cepdnaclk/e21-3yp-SlideSense/docs/assets/about/about-slidesense.png

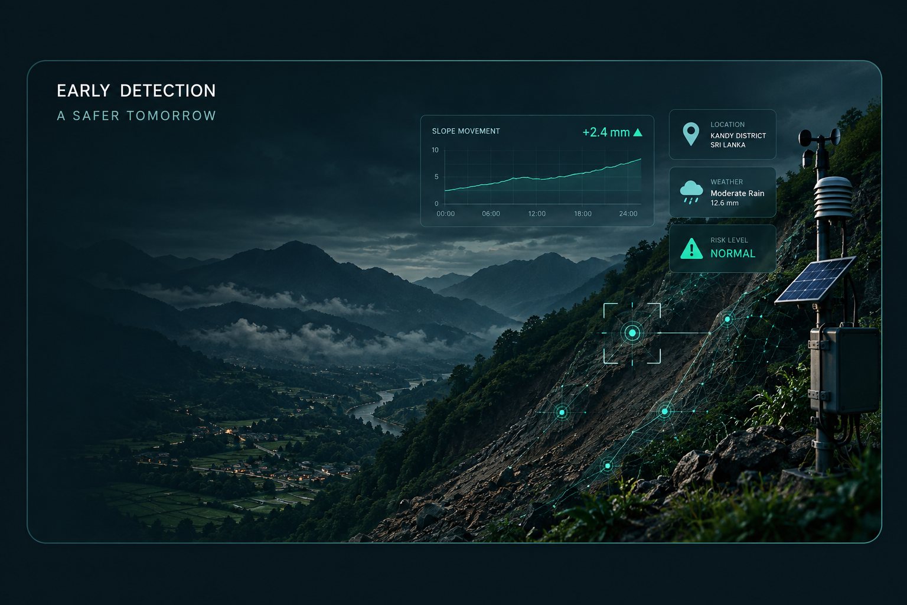
docs/assets/about/about-slidesense.png
