cepdnaclk/e21-3yp-SlideSense/docs/assets/Compenents/aws-iot-core.png

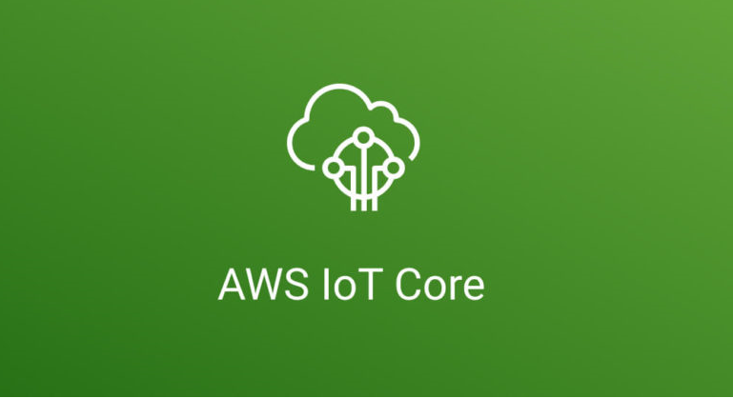
docs/assets/Compenents/aws-iot-core.png
