cepdnaclk/e21-3yp-SlideSense/docs/assets/Compenents/esp32.jpg

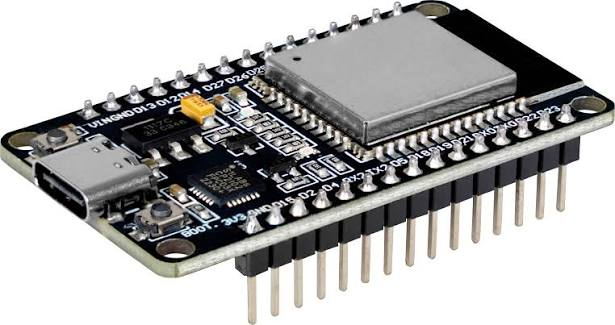
docs/assets/Compenents/esp32.jpg
