cepdnaclk/e21-3yp-SlideSense/docs/assets/Compenents/GPS_module.jpg

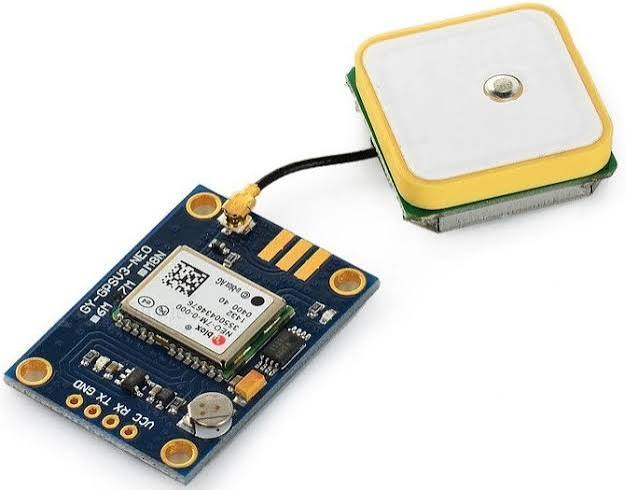
docs/assets/Compenents/GPS_module.jpg
