cepdnaclk/e21-3yp-SlideSense/docs/assets/Compenents/microphone.jpg

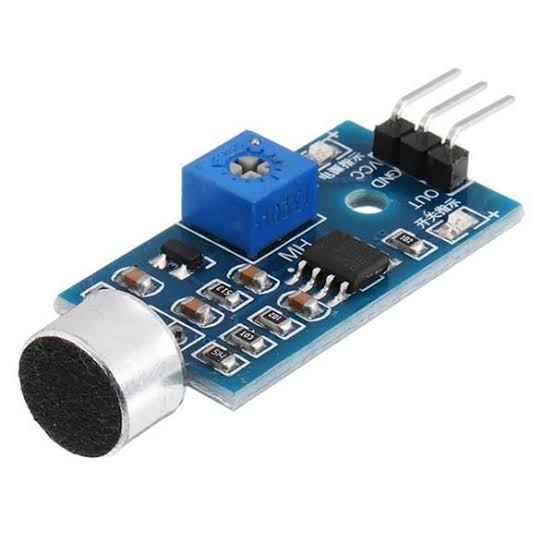
docs/assets/Compenents/microphone.jpg
