cepdnaclk/e21-3yp-SlideSense/docs/assets/Compenents/soli-moisture.jpg

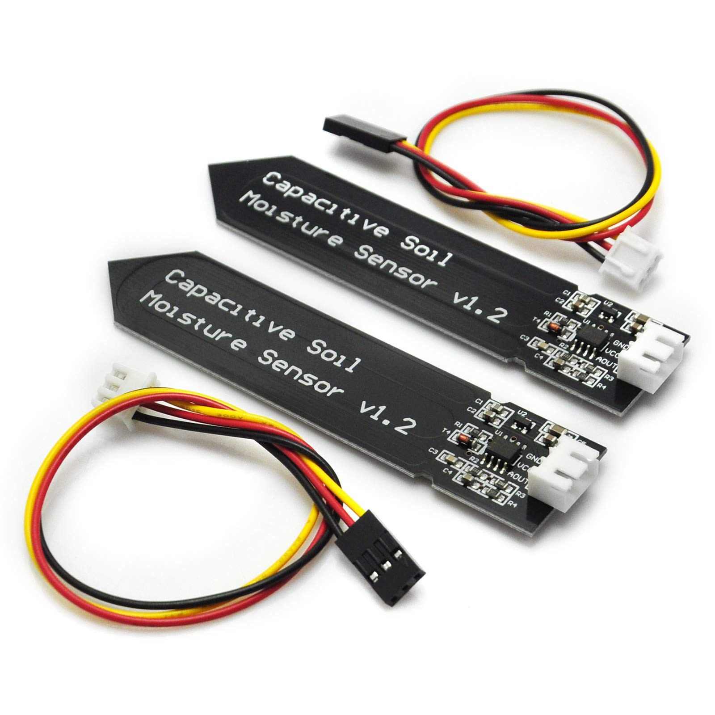
docs/assets/Compenents/soli-moisture.jpg
