cepdnaclk/e21-3yp-SlideSense/docs/assets/Compenents/tilt_sesnsor.webp

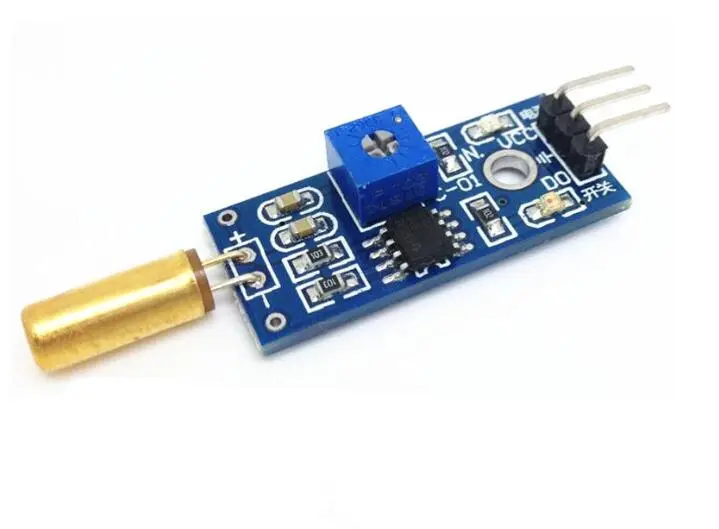
docs/assets/Compenents/tilt_sesnsor.webp
