cepdnaclk/e21-3yp-SlideSense/docs/assets/dashboard/image.png

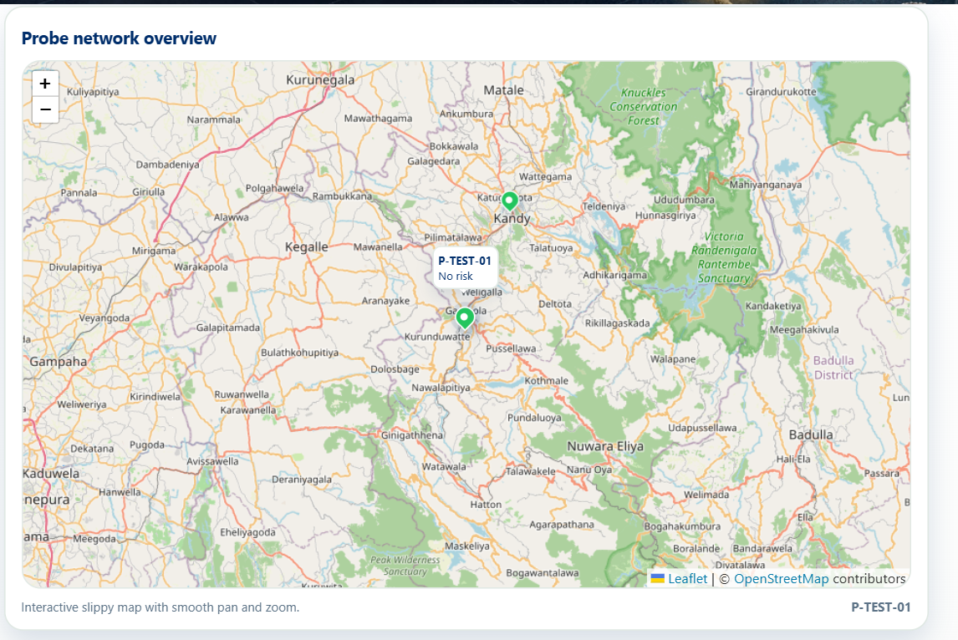
docs/assets/dashboard/image.png
