cepdnaclk/e21-3yp-SlideSense/docs/assets/dashboard/main.png

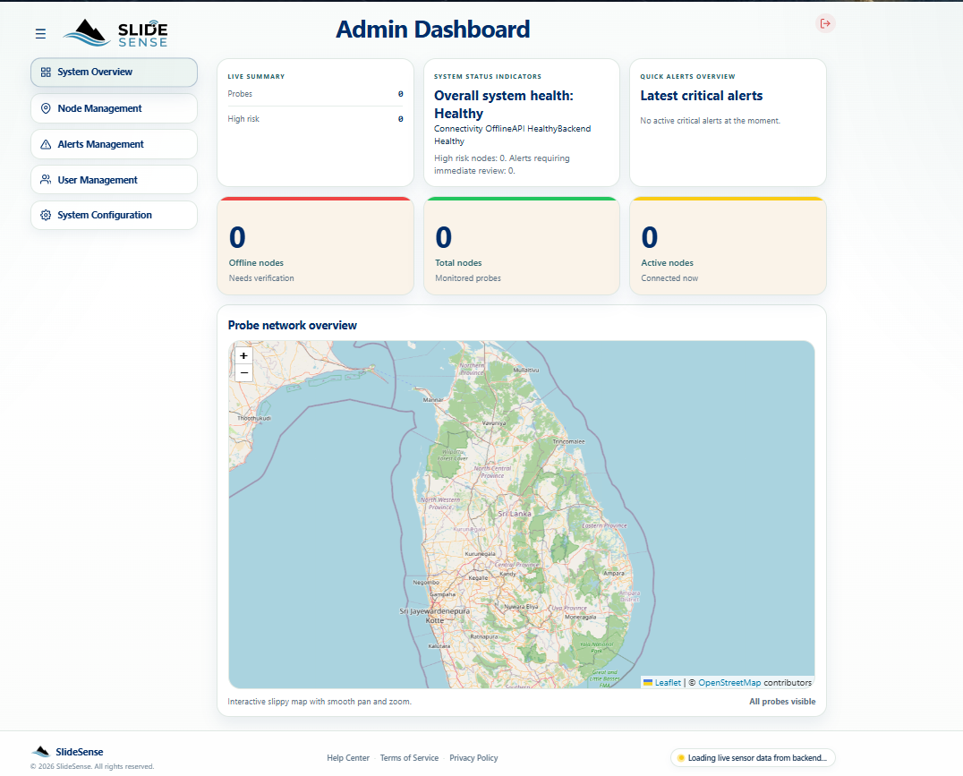
docs/assets/dashboard/main.png
