cepdnaclk/e21-3yp-SlideSense/docs/assets/final_product/probe.png

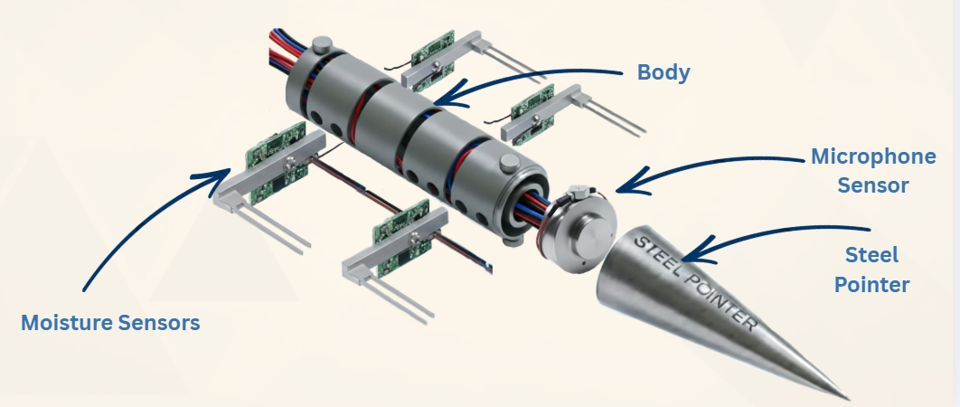
docs/assets/final_product/probe.png
