cepdnaclk/e21-3yp-SlideSense/docs/assets/final_product/solar.jpeg

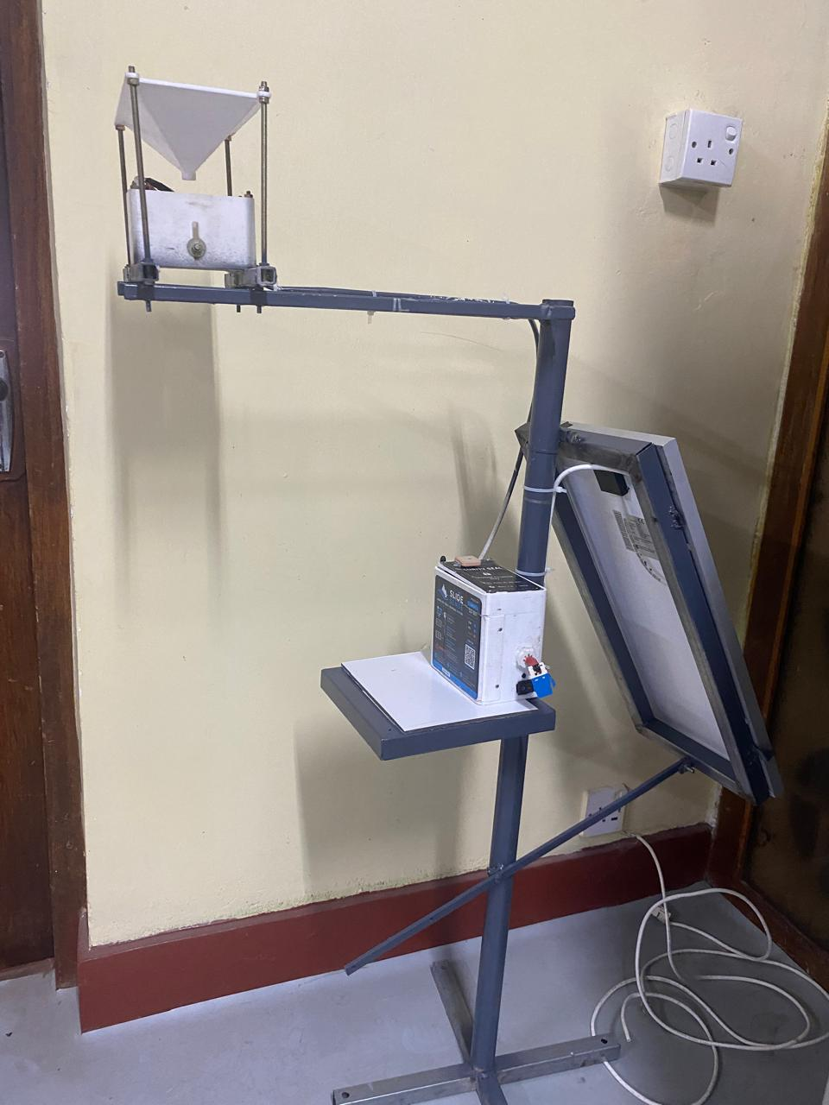
docs/assets/final_product/solar.jpeg
