cepdnaclk/e21-3yp-SlideSense/docs/assets/hero-background.png

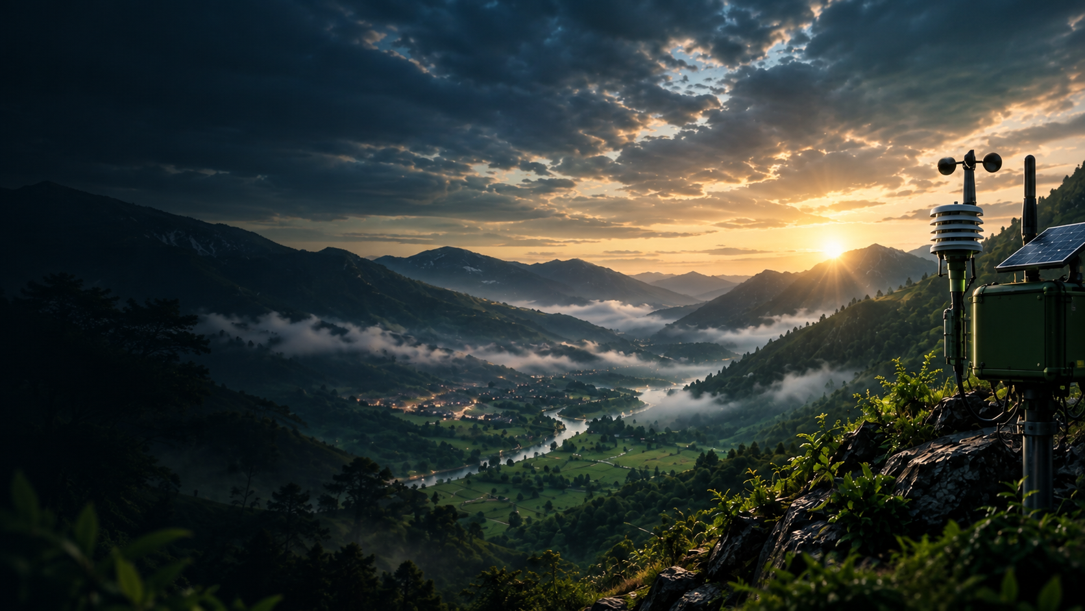
docs/assets/hero-background.png
