cepdnaclk/e21-3yp-SlideSense/docs/assets/images/historical_sensor_analytics.png

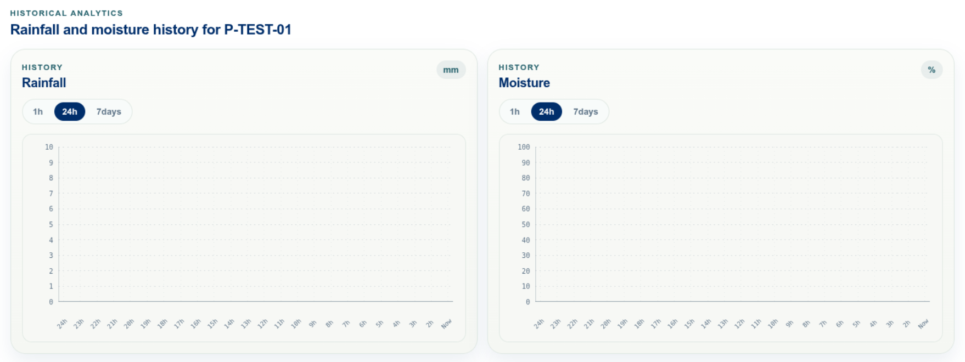
docs/assets/images/historical_sensor_analytics.png
