cepdnaclk/e21-3yp-SlideSense/docs/assets/images/hole.jpeg

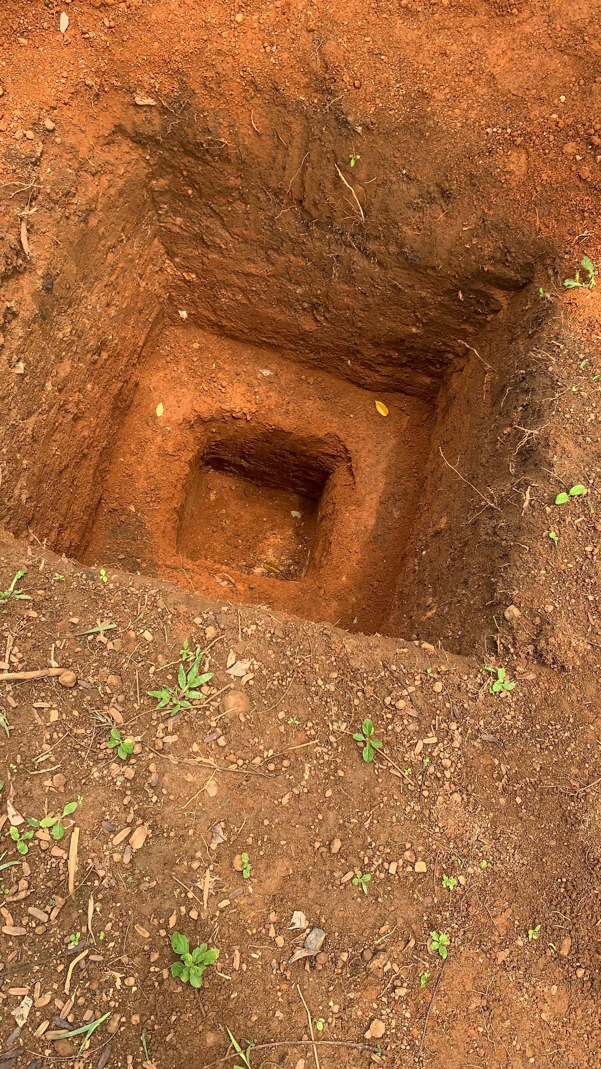
docs/assets/images/hole.jpeg
