cepdnaclk/e21-3yp-SlideSense/docs/assets/images/probe_in_hole.jpeg

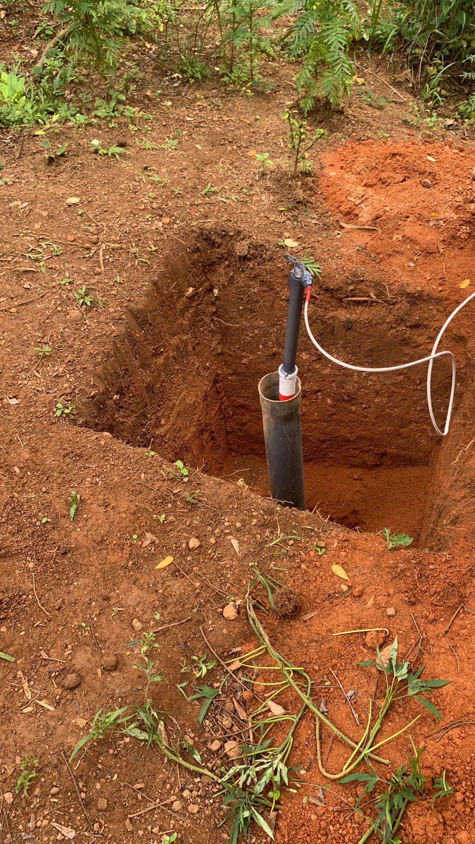
docs/assets/images/probe_in_hole.jpeg
