cepdnaclk/e21-3yp-SlideSense/docs/assets/images/rain_gauge.jpeg

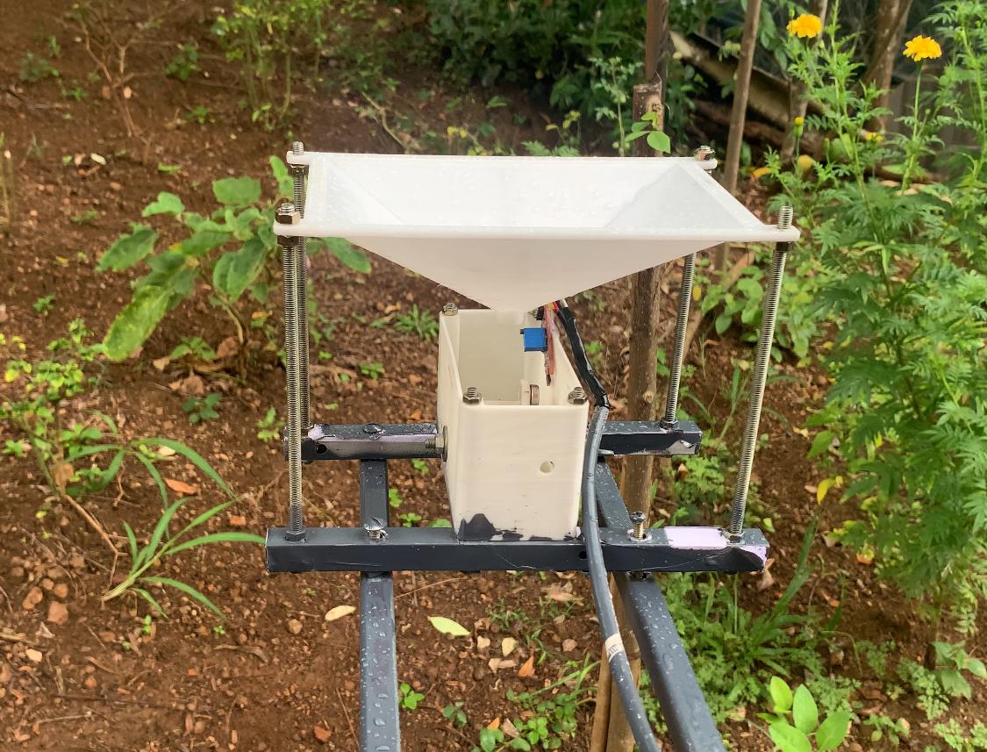
docs/assets/images/rain_gauge.jpeg
