cepdnaclk/e21-3yp-SlideSense/docs/assets/images/team_final.jpeg

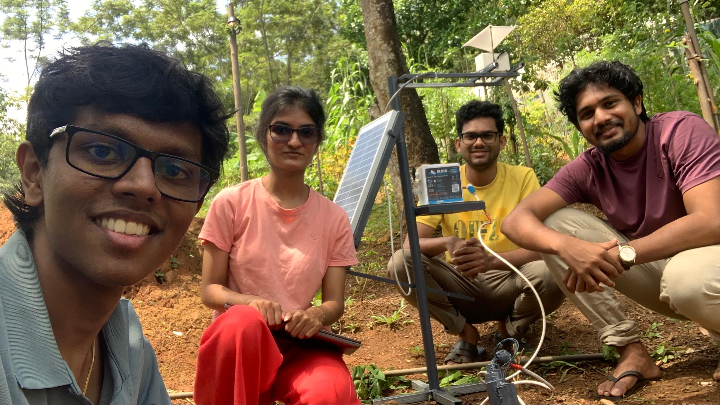
docs/assets/images/team_final.jpeg
