cepdnaclk/e21-3yp-SlideSense/docs/assets/images/work_bench_1.jpeg

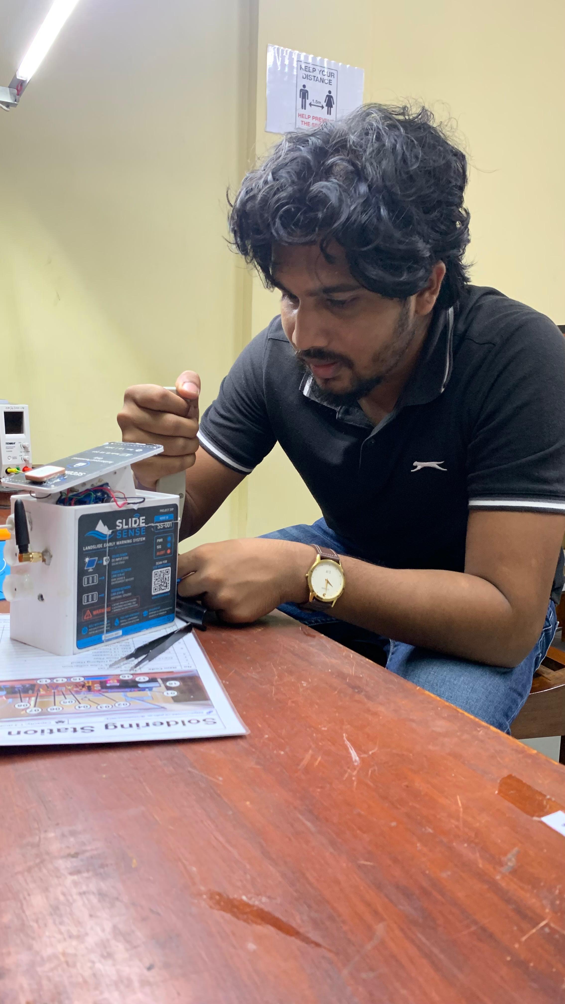
docs/assets/images/work_bench_1.jpeg
