cepdnaclk/e21-3yp-SlideSense/docs/assets/LoadBackground.jpg

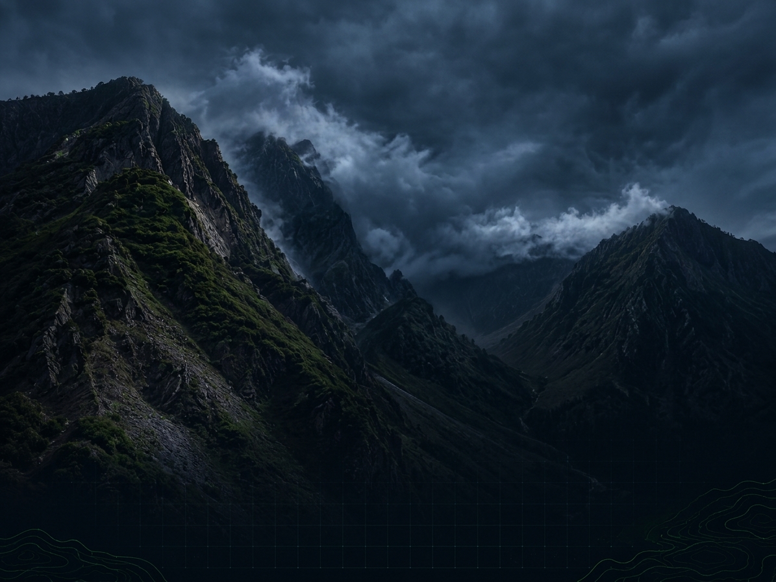
docs/assets/LoadBackground.jpg
