cepdnaclk/e21-3yp-SlideSense/docs/assets/videos/WhatsApp Image 2026-09-15 at 19.24.26.jpeg

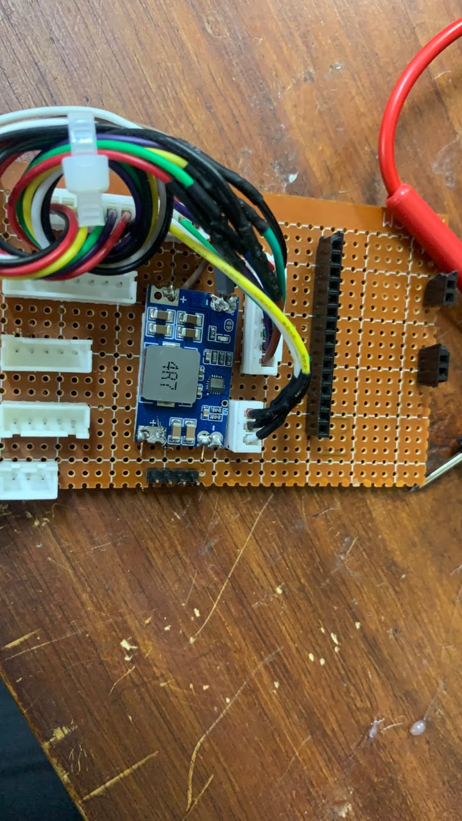
docs/assets/videos/WhatsApp Image 2026-09-15 at 19.24.26.jpeg
