cepdnaclk/e21-3yp-SlideSense/docs/data/thumbnail.jpg

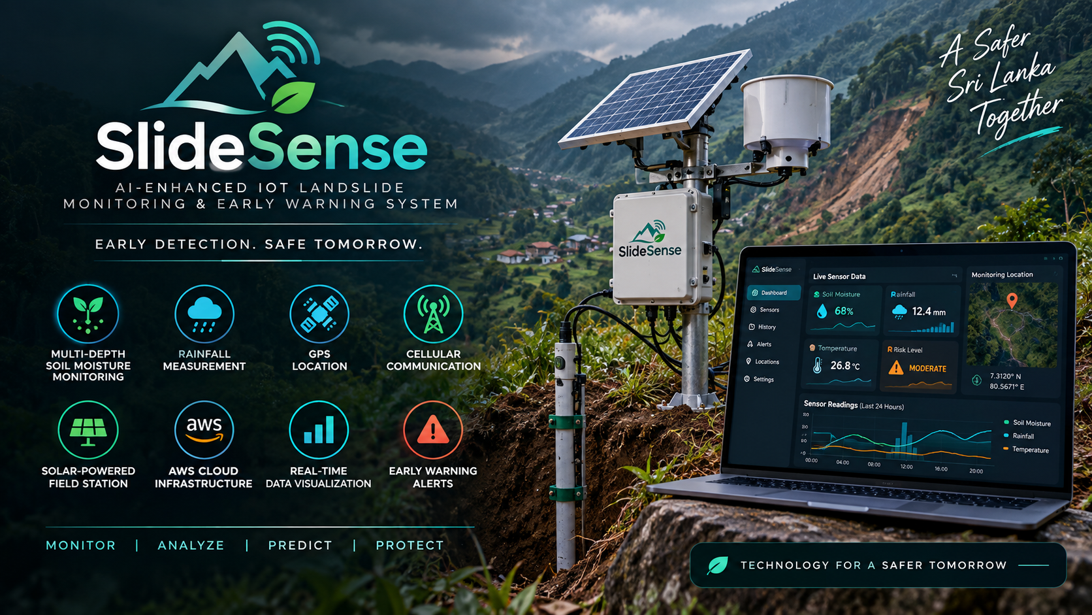
docs/data/thumbnail.jpg
