cepdnaclk/e21-3yp-SlideSense/docs/images/ESP32_Pin_Diagram.png

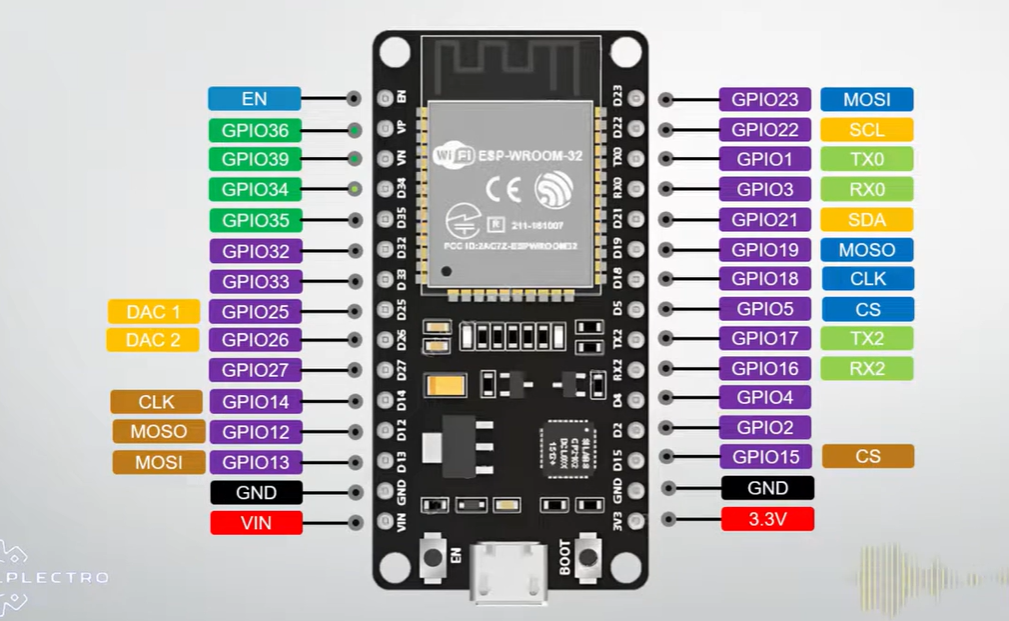
docs/images/ESP32_Pin_Diagram.png
