cepdnaclk/e21-3yp-SlideSense/docs/images/heo-background.jpg

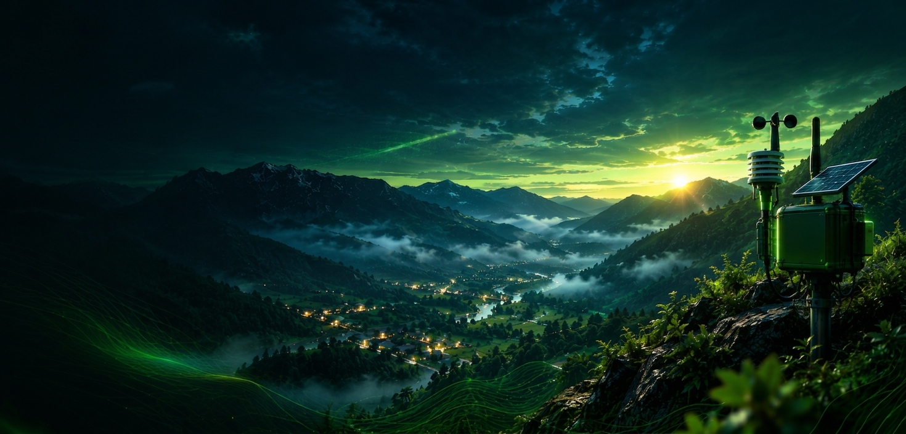
docs/images/heo-background.jpg
