cepdnaclk/e21-3yp-SlideSense/docs/images/image_2026-02-12_193107574.png

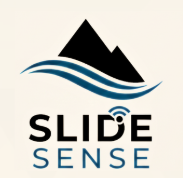
docs/images/image_2026-02-12_193107574.png
