cepdnaclk/e21-3yp-SlideSense/docs/images/RainGauge_Bucket.png

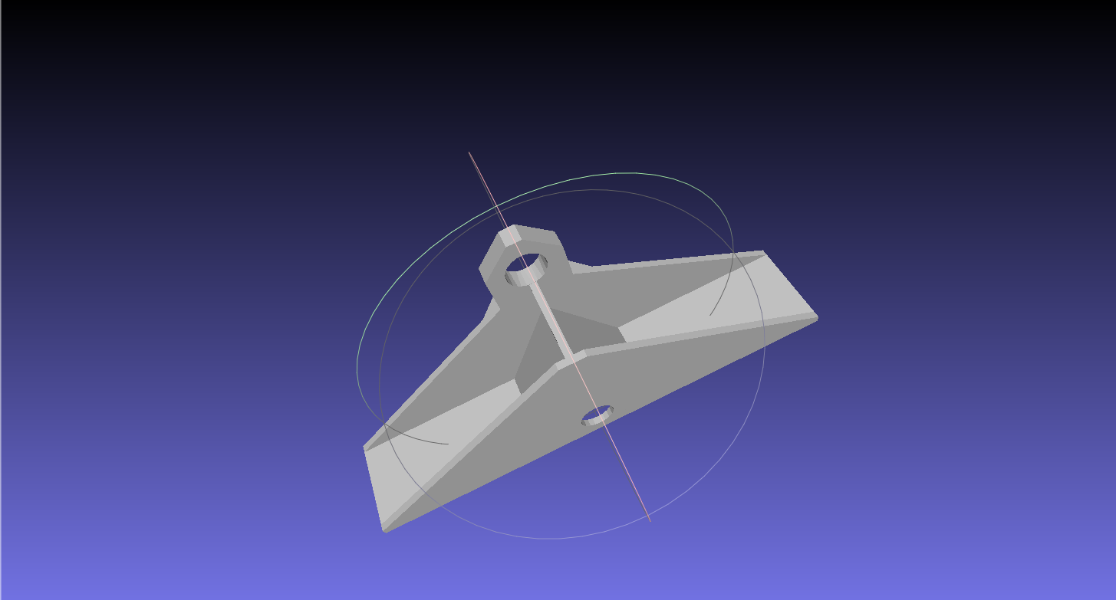
docs/images/RainGauge_Bucket.png
