cepdnaclk/e21-3yp-SlideSense/docs/images/RainGauge_Funnel.png

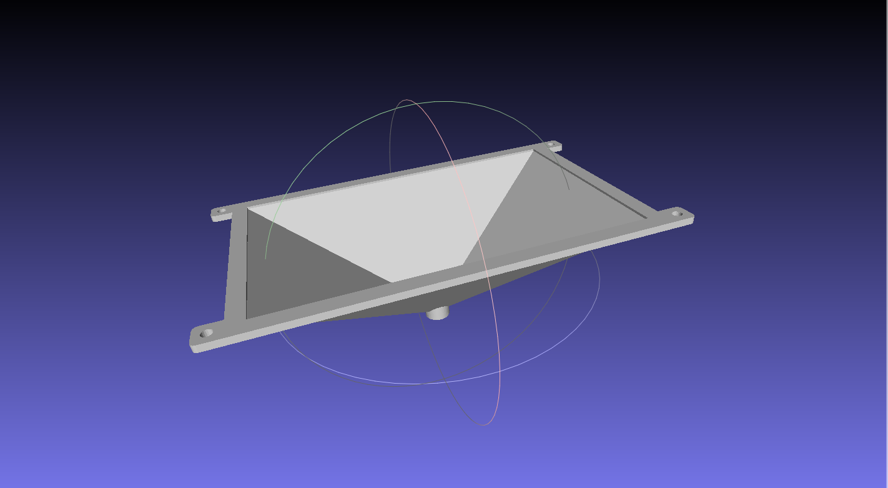
docs/images/RainGauge_Funnel.png
