cepdnaclk/e21-3yp-SlideSense/docs/images/Screenshot 2026-02-12 193805.png

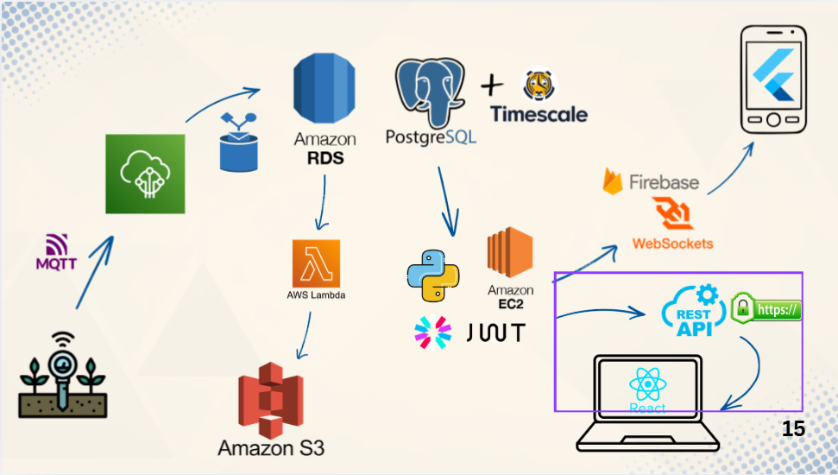
docs/images/Screenshot 2026-02-12 193805.png
