cepdnaclk/e21-3yp-SlideSense/docs/assets/images/setup_full.jpeg

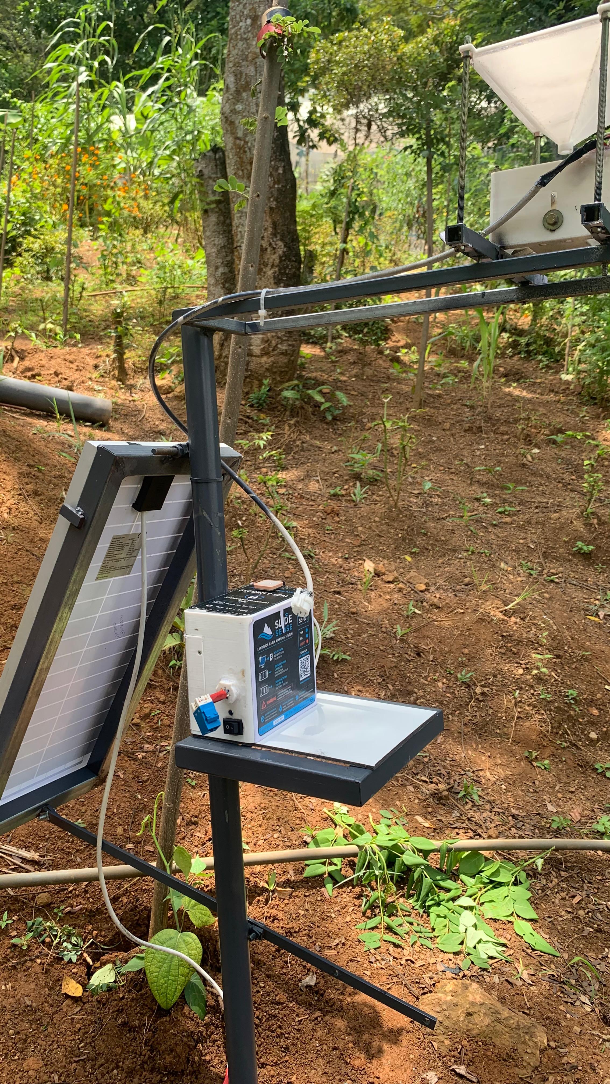
docs/assets/images/setup_full.jpeg
