cepdnaclk/e21-3yp-SlideSense/docs/assets/videos/test01.jpeg

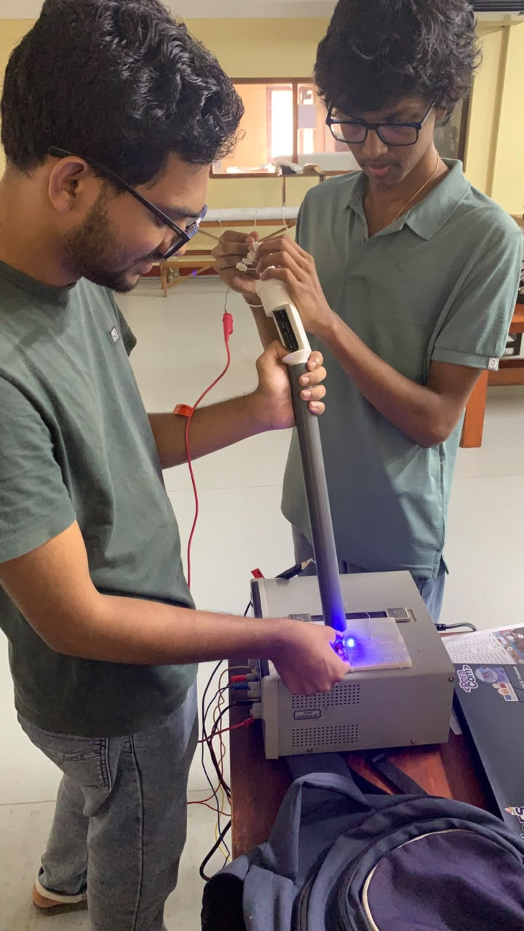
docs/assets/videos/test01.jpeg
