cepdnaclk/e21-3yp-SlideSense/docs/assets/videos/test02.jpeg

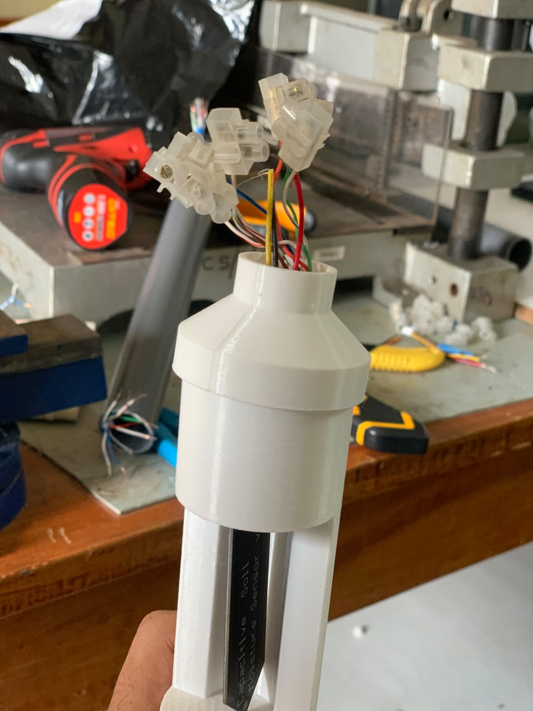
docs/assets/videos/test02.jpeg
