cepdnaclk/e21-3yp-SlideSense/docs/assets/videos/test03.jpeg

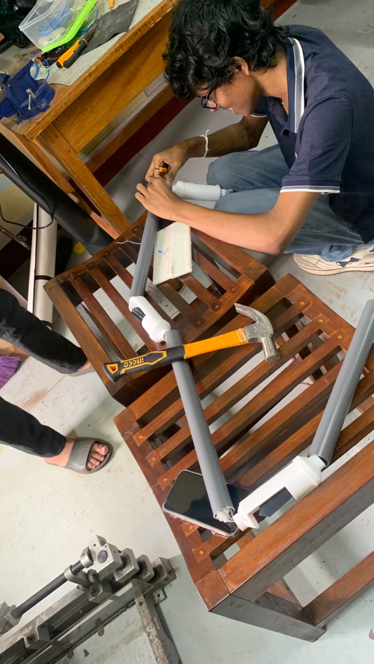
docs/assets/videos/test03.jpeg
