cepdnaclk/e21-3yp-SlideSense/ESP32_Scripts/SOIL MOISTURE/Sensor_1_Calibrate.cpp

#include <Arduino.h>

#define MOISTURE_SENSOR_PIN 35

const int dry = 3200;  // dry value
const int wet = 2000;   // wet value

void setup() {
  Serial.begin(115200);

  pinMode(MOISTURE_SENSOR_PIN, INPUT);

  Serial.println("Soil Moisture Sensor Started (ESP32)");
}

void loop() {

  int sensorValue = analogRead(MOISTURE_SENSOR_PIN);

  float moisturePercent = map(sensorValue, wet, dry, 100, 0);

  Serial.print("Raw Value: ");
  Serial.print(sensorValue);

  Serial.print("  | Moisture: ");
  Serial.print(moisturePercent);
  Serial.println("%");

  delay(1000);  // update every second
}
